toammann/Multilayer_SMA2Microstrip/FreeCAD_Aisler6LayerHD_SMA_v2/conn_outer_body.stl

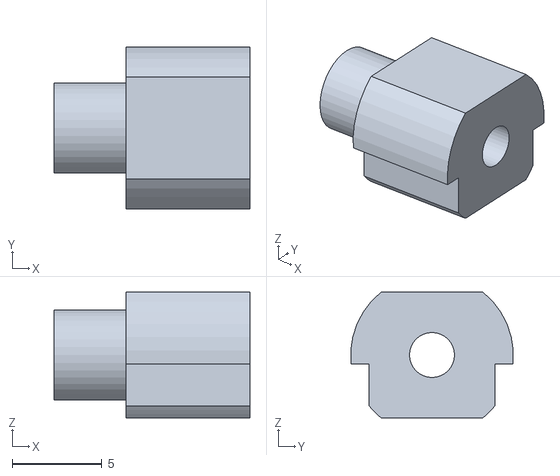
[picture p35: CAD file, 2023-11-16]
FreeCAD_Aisler6LayerHD_SMA_v2/conn_outer_body.stl
10.9 x 9.03 x 7.00
