toammann/Multilayer_SMA2Microstrip/FreeCAD_Aisler6LayerHD_SMA_v2/l02_gnd.stl

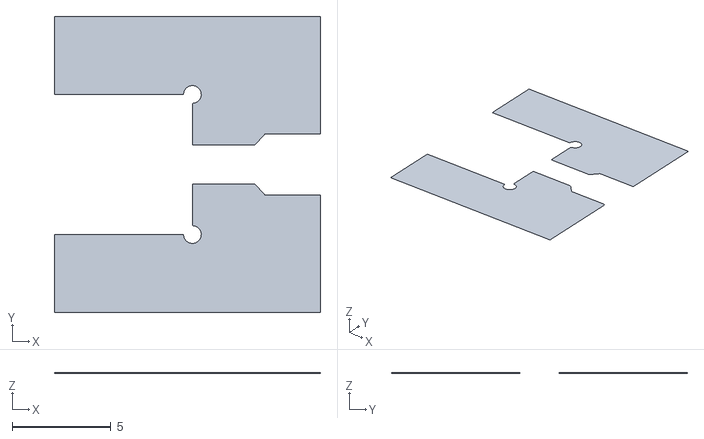
[picture p36: CAD file, 2023-11-16]
FreeCAD_Aisler6LayerHD_SMA_v2/l02_gnd.stl
13.5 x 15.0 x 0.035
