toammann/Multilayer_SMA2Microstrip/FreeCAD_Aisler6LayerHD_SMA_v2/Aisler6LayerHD_SMA_v2_L04.dxf

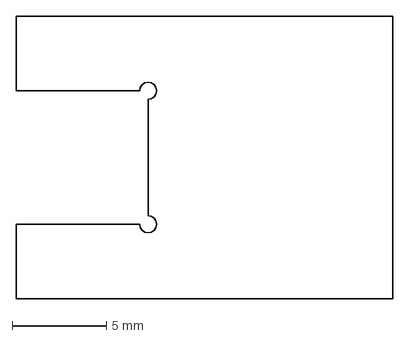
[picture p37: CAD file, 2023-11-16]
FreeCAD_Aisler6LayerHD_SMA_v2/Aisler6LayerHD_SMA_v2_L04.dxf
20.0 x 15.0 mm
