toammann/Multilayer_SMA2Microstrip/FreeCAD_Aisler6LayerHD_SMA_v2/Aisler6LayerHD_SMA_v2_L03.dxf

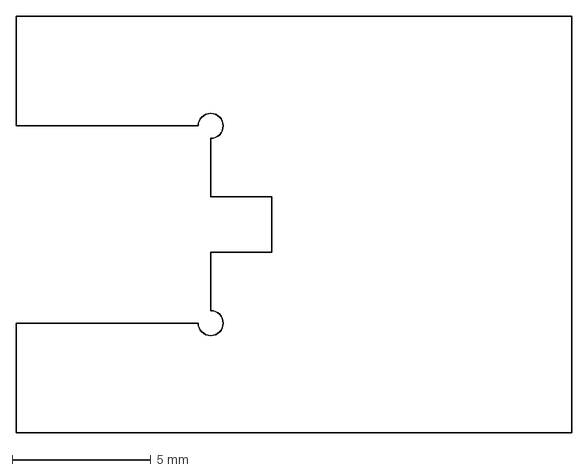
[picture p38: CAD file, 2023-11-16]
FreeCAD_Aisler6LayerHD_SMA_v2/Aisler6LayerHD_SMA_v2_L03.dxf
20.0 x 15.0 mm
