toammann/Multilayer_SMA2Microstrip/FreeCAD_Aisler6LayerHD_SMA_v2/edge_plating.stl

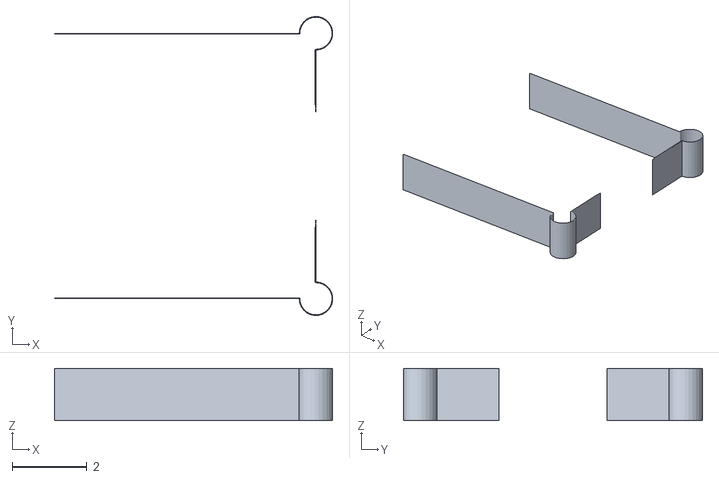
[picture p39: CAD file, 2023-11-16]
FreeCAD_Aisler6LayerHD_SMA_v2/edge_plating.stl
7.45 x 8.00 x 1.40
