toammann/Multilayer_SMA2Microstrip/FreeCAD_Aisler6LayerHD_SMA_v2/solder_top_pin.stl

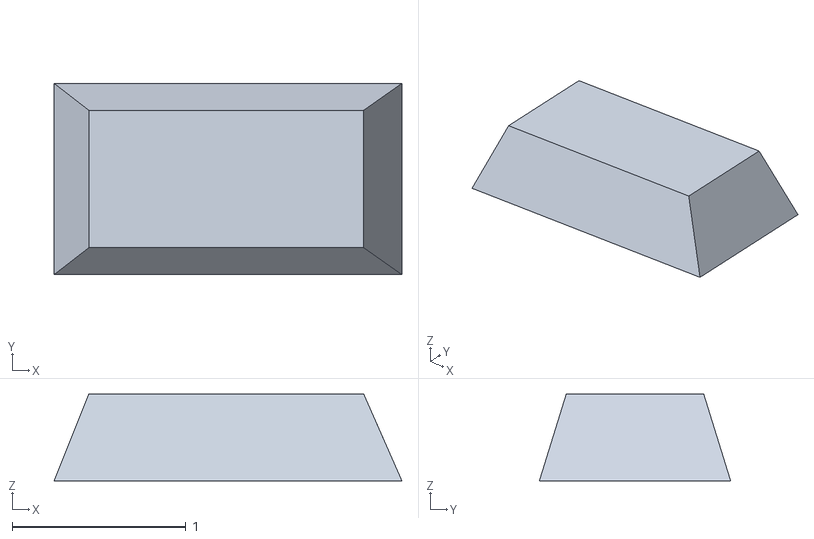
[picture p40: CAD file, 2023-06-05]
FreeCAD_Aisler6LayerHD_SMA_v2/solder_top_pin.stl
2.00 x 1.10 x 0.5
