toammann/Multilayer_SMA2Microstrip/FreeCAD_Aisler6LayerHD_SMA_v2/solder_bot.stl

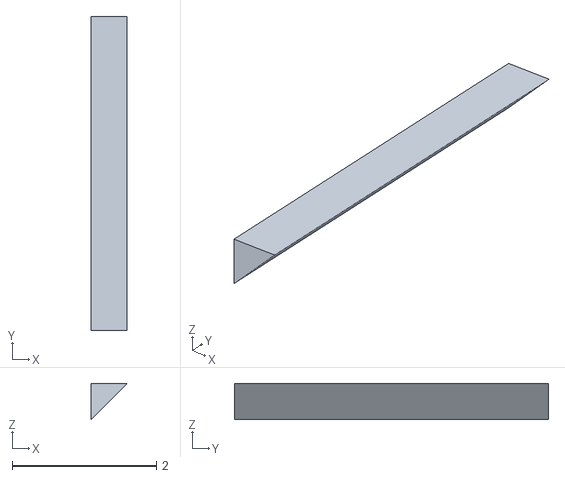
[picture p41: CAD file, 2023-06-05]
FreeCAD_Aisler6LayerHD_SMA_v2/solder_bot.stl
0.5 x 4.35 x 0.5
