toammann/Multilayer_SMA2Microstrip/FreeCAD_Aisler6LayerHD_SMA_v2/l01_rf_trace.stl

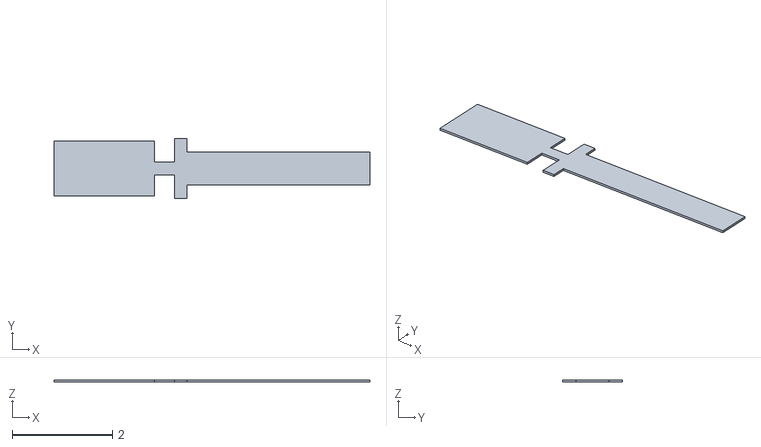
[picture p42: CAD file, 2023-06-05]
FreeCAD_Aisler6LayerHD_SMA_v2/l01_rf_trace.stl
6.30 x 1.20 x 0.04
