toammann/Multilayer_SMA2Microstrip/FreeCAD_Aisler6LayerHD_SMA_v2/Aisler6LayerHD_SMA_v2_EdgePlating.dxf

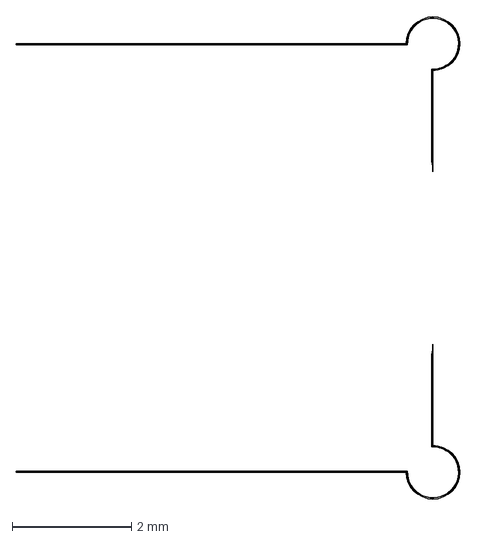
[picture p43: CAD file, 2023-06-05]
FreeCAD_Aisler6LayerHD_SMA_v2/Aisler6LayerHD_SMA_v2_EdgePlating.dxf
7.47 x 8.13 mm
