toammann/Multilayer_SMA2Microstrip/FreeCAD_Aisler6LayerHD_SMA_v2/via_fence.stl

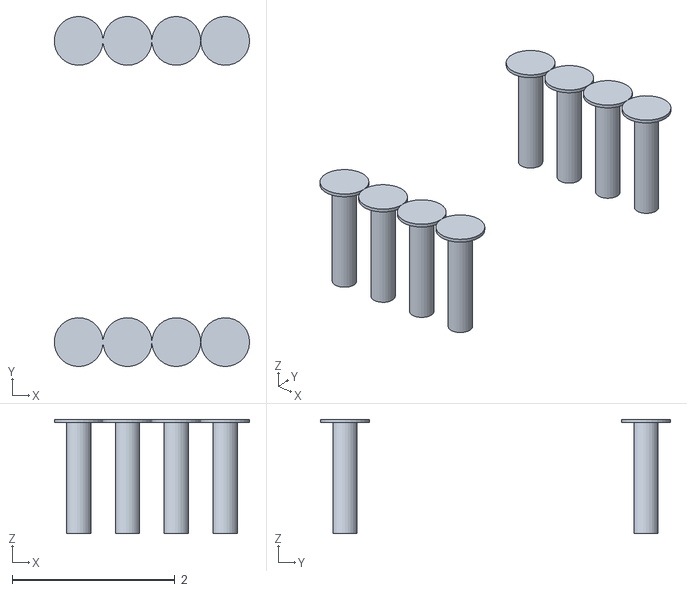
[picture p44: CAD file, 2023-06-05]
FreeCAD_Aisler6LayerHD_SMA_v2/via_fence.stl
2.40 x 4.30 x 1.40
