toammann/Multilayer_SMA2Microstrip/FreeCAD_Aisler6LayerHD_SMA_v2/l03_neg.stl

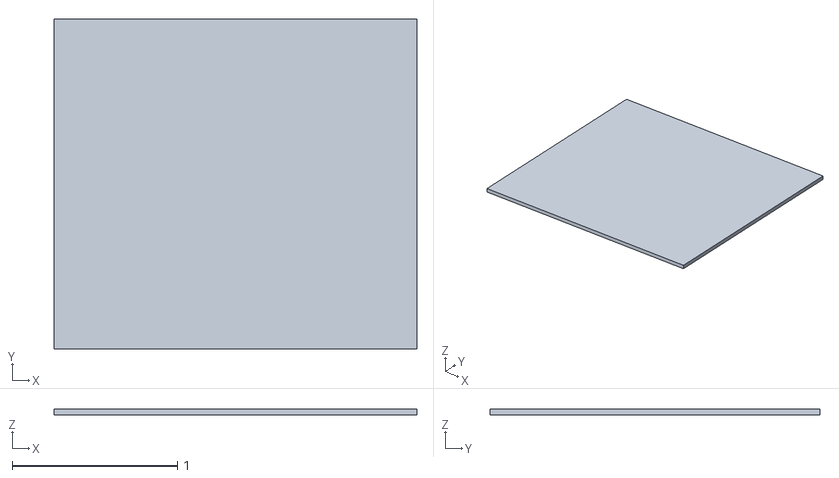
[picture p45: CAD file, 2023-06-05]
FreeCAD_Aisler6LayerHD_SMA_v2/l03_neg.stl
2.20 x 2.00 x 0.035
