toammann/Multilayer_SMA2Microstrip/FreeCAD_Aisler6LayerHD_SMA_v2/via_trans.stl

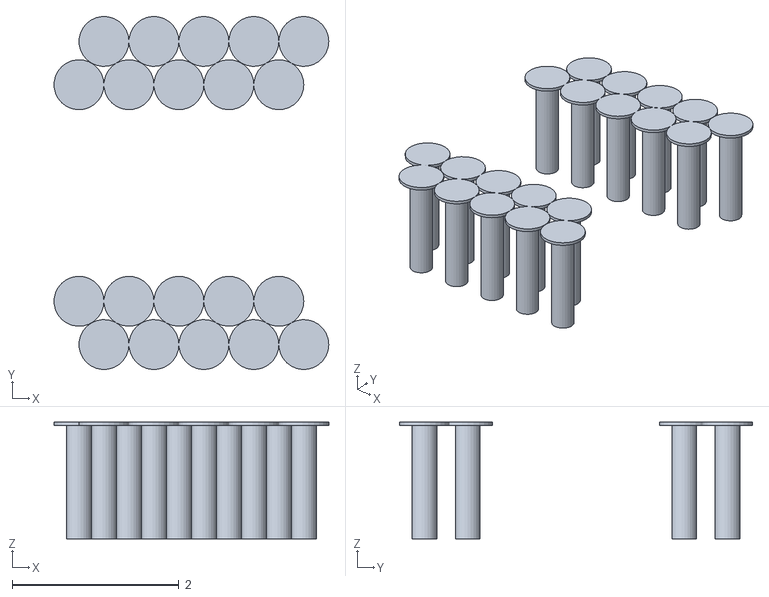
[picture p46: CAD file, 2023-06-05]
FreeCAD_Aisler6LayerHD_SMA_v2/via_trans.stl
3.30 x 4.24 x 1.40
