toammann/Multilayer_SMA2Microstrip/KiCAD_Rosenberger_32K242-40ML5_testboard_v2/rosenberger_32K242-40ML5_testboard_v2.kicad_sch

## KiCad design KiCAD_Rosenberger_32K242-40ML5_testboard_v2/rosenberger_32K242-40ML5_testboard_v2.kicad_sch (2023-06-05)

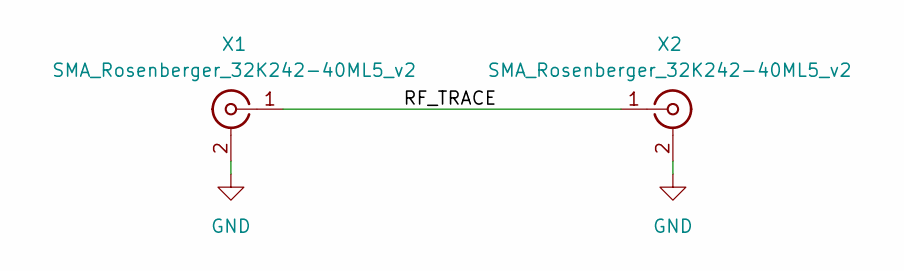
[picture p48: schematic rosenberger_32K242-40ML5_testboard_v2.kicad_sch]

Parts:
X1, X2: SMA_Rosenberger_32K242-40ML5_v2; Rosenberger_32K242-40ML5v2; Manufacturer Part Number 32K242-40ML5

Connections:
GND: X1.2 (Ext), X2.2 (Ext)
RF_TRACE: X1.1 (In), X2.1 (In)
